kimf/hodgepodge-keyboard/Keylayout/2025-12-05/2025-12-05-HodgePodge.png

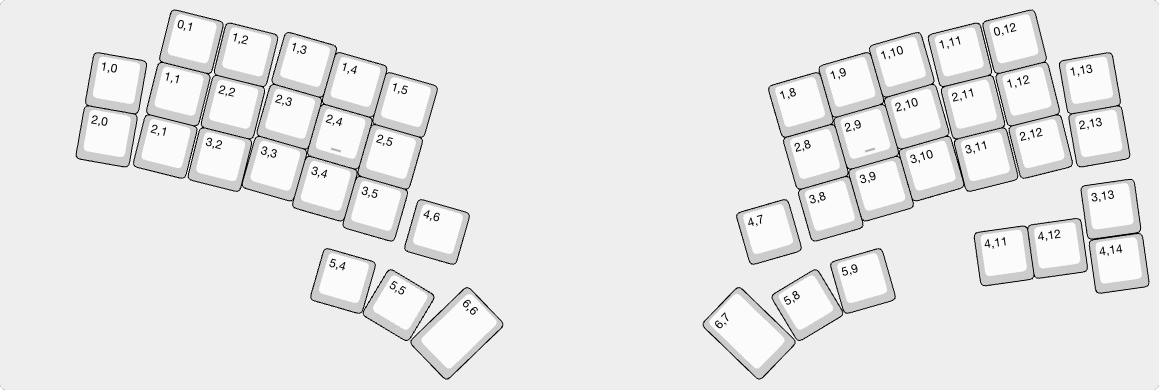
Keylayout/2025-12-05/2025-12-05-HodgePodge.png
