kimf/hodgepodge-keyboard/Keylayout/2025-12-08/2025-12-08-HodgePodge.png

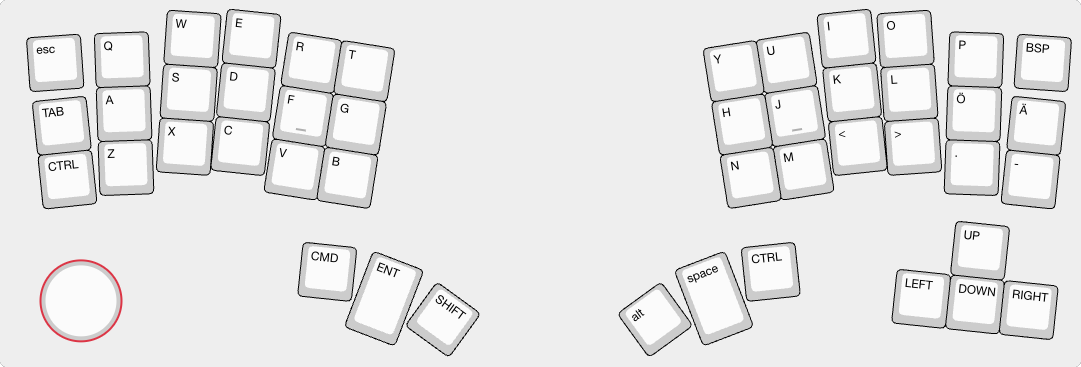
Keylayout/2025-12-08/2025-12-08-HodgePodge.png
