kimf/hodgepodge-keyboard/Keylayout/HodgePodge.png

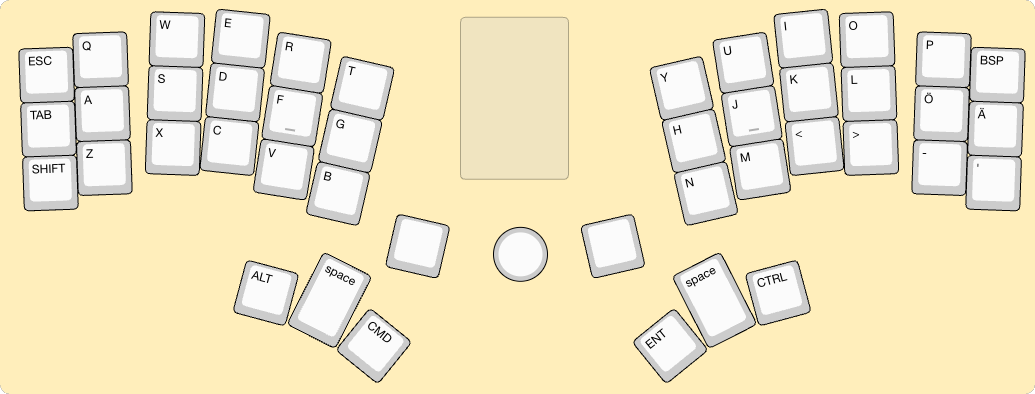
Keylayout/HodgePodge.png
