kimf/hodgepodge-keyboard/3D-files/STEP/_PARTS/EC11-boxy.step

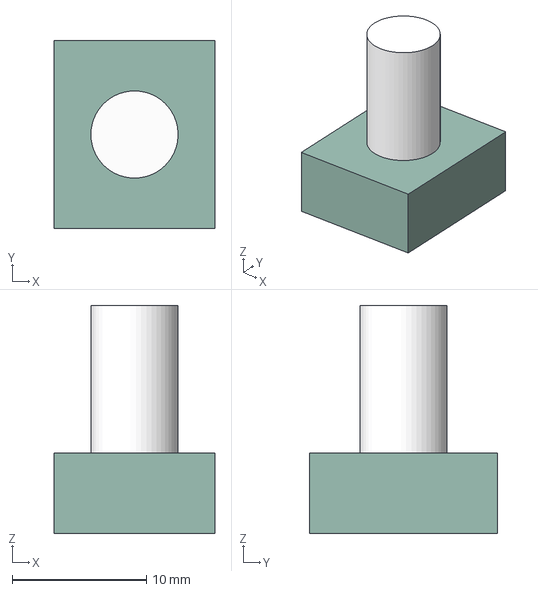
[picture p25: CAD file, 2026-01-12]
3D-files/STEP/_PARTS/EC11-boxy.step
12.0 x 14.0 x 17.0 mm
