kimf/hodgepodge-keyboard/3D-files/STL/RightBottomPlate.stl

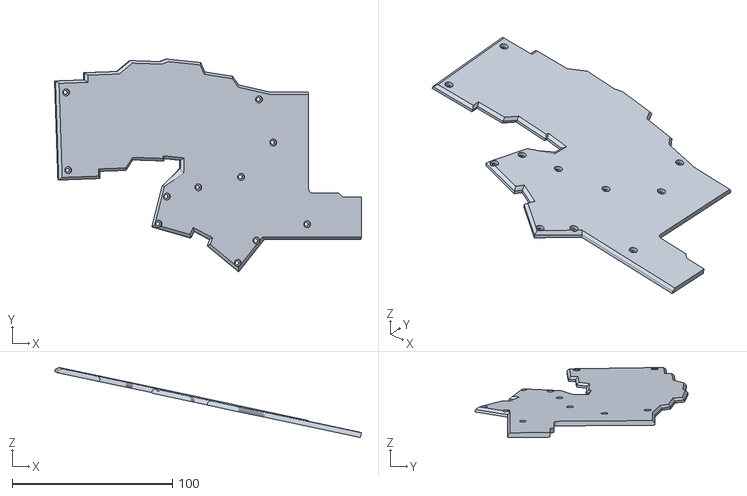
[picture p26: CAD file, 2026-01-12]
3D-files/STL/RightBottomPlate.stl
191.8 x 133.0 x 43.8
