kimf/hodgepodge-keyboard/3D-files/testing-layout-and-choc-holders/HodgePodge-BasePlate-Left.stl

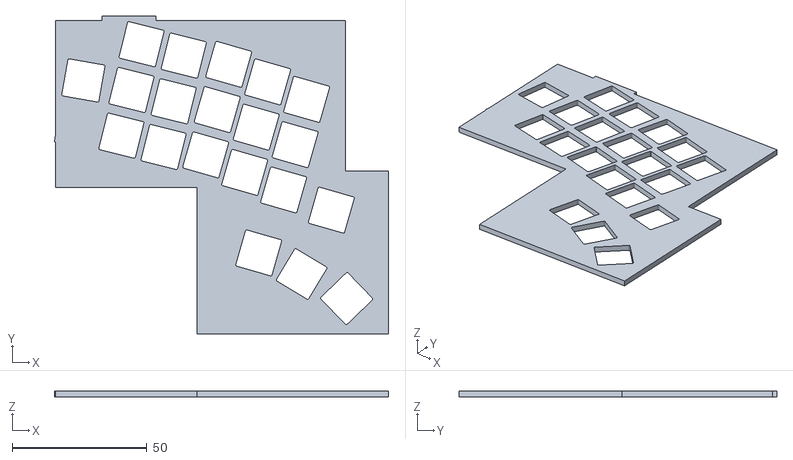
[picture p27: CAD file, 2026-01-12]
3D-files/testing-layout-and-choc-holders/HodgePodge-BasePlate-Left.stl
124.1 x 118.1 x 2.20
