kimf/hodgepodge-keyboard/3D-files/STL/LeftBottomPlate.stl

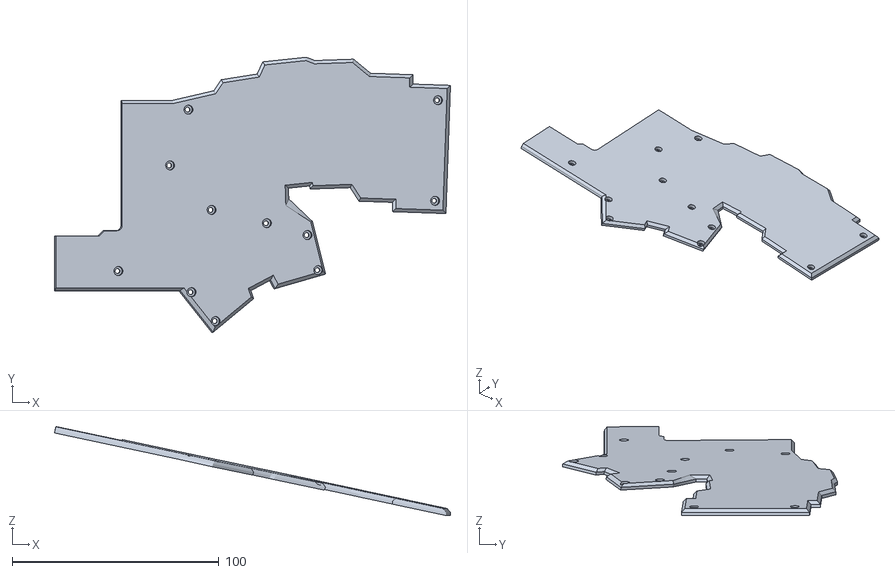
[picture p28: CAD file, 2026-01-12]
3D-files/STL/LeftBottomPlate.stl
191.3 x 133.1 x 43.0
