kimf/hodgepodge-keyboard/3D-files/testing-layout-and-choc-holders/HodgePodge-ChocTest.stl

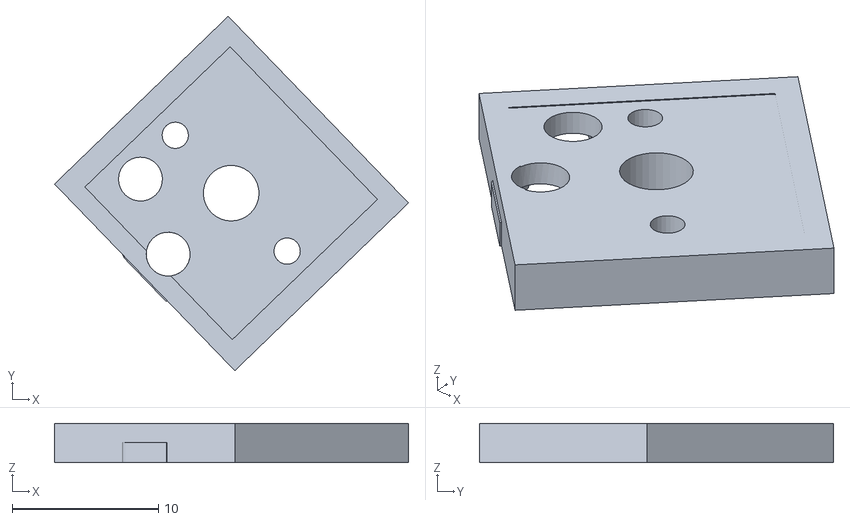
[picture p29: CAD file, 2026-01-12]
3D-files/testing-layout-and-choc-holders/HodgePodge-ChocTest.stl
24.2 x 24.2 x 2.70
