kimf/hodgepodge-keyboard/3D-files/testing-layout-and-choc-holders/HodgePodge-BasePlate-Right.stl

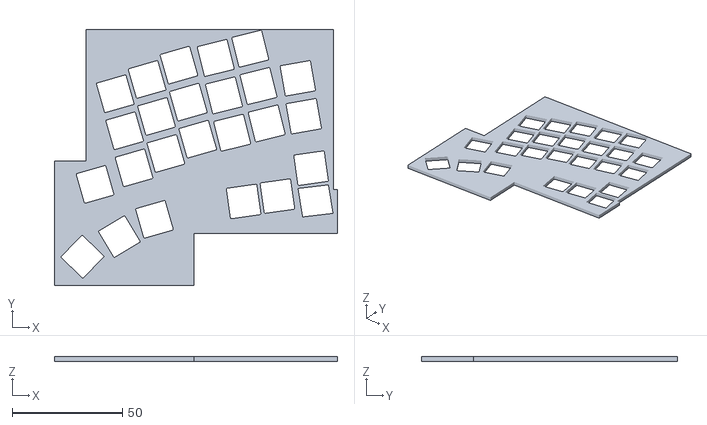
[picture p30: CAD file, 2026-01-12]
3D-files/testing-layout-and-choc-holders/HodgePodge-BasePlate-Right.stl
128.6 x 116.4 x 2.20
