kimf/hodgepodge-keyboard/3D-files/STL/nRF5340 DK Case.stl

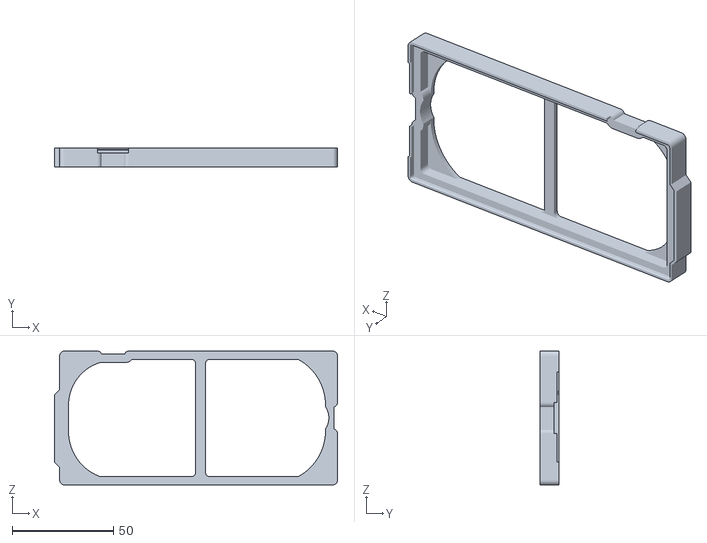
[picture p31: CAD file, 2026-01-12]
3D-files/STL/nRF5340 DK Case.stl
139.7 x 9.60 x 66.1
