kimf/hodgepodge-keyboard/images/soldering-rows-and-columns.jpg

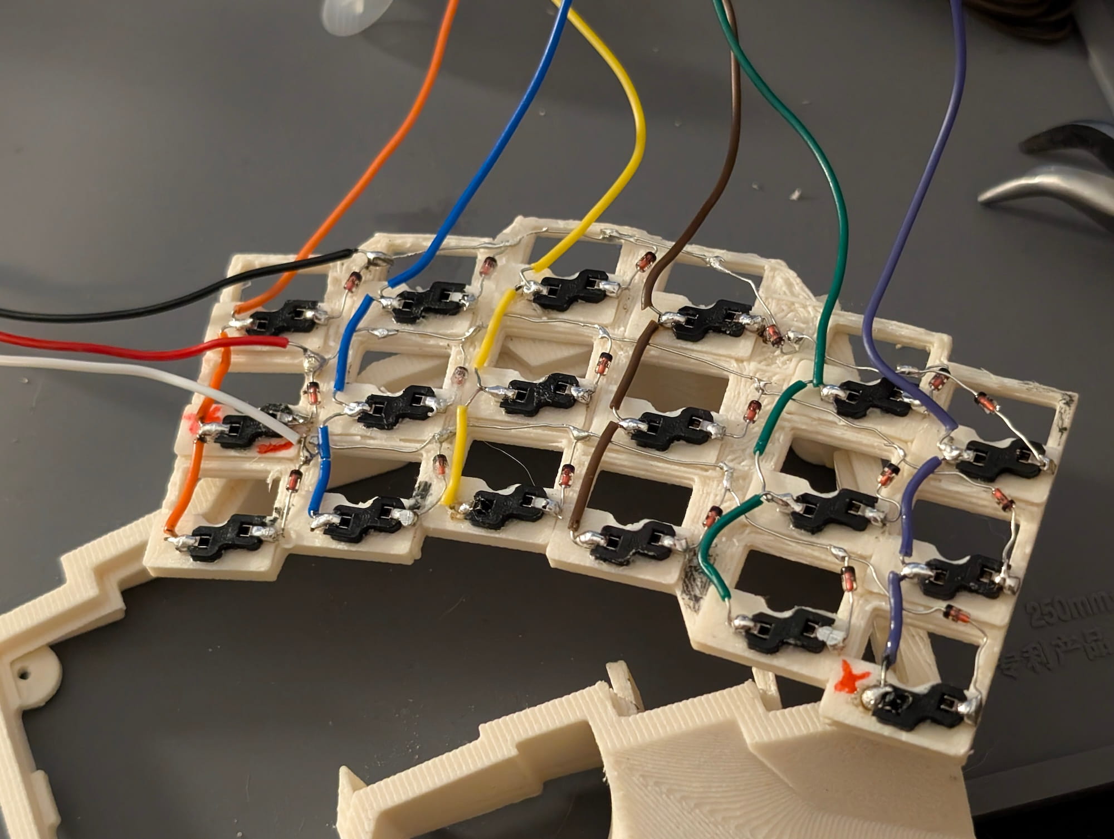
images/soldering-rows-and-columns.jpg
