kimf/hodgepodge-keyboard/images/layout-testing.jpg

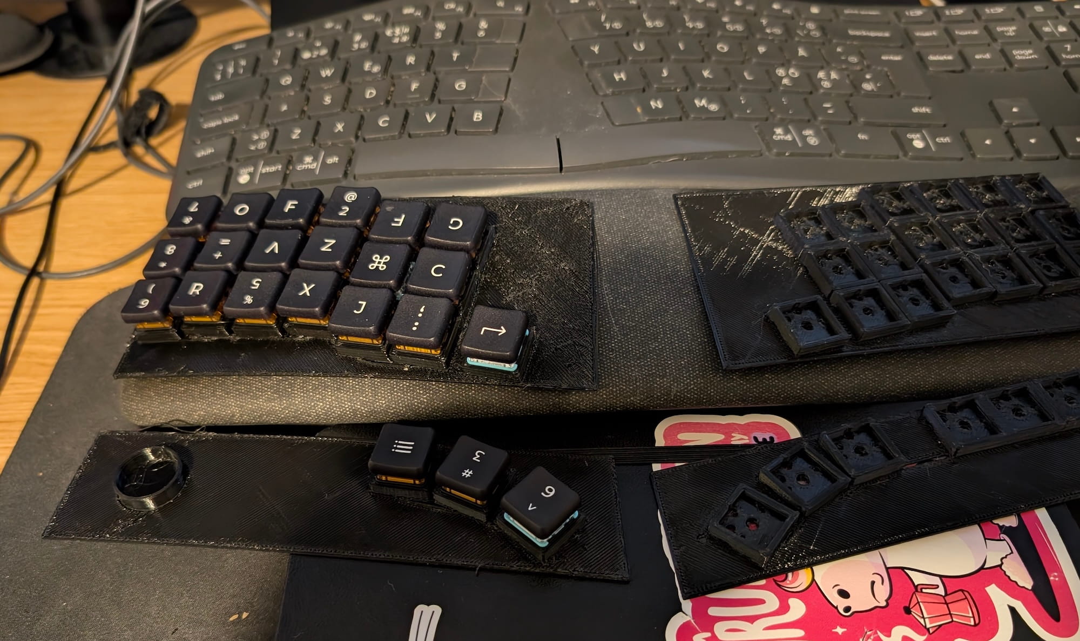
images/layout-testing.jpg
